pete-restall/KitchenLedStrips/doc/bench/led-data-streams/rgb-000000-noslew-470pF.png

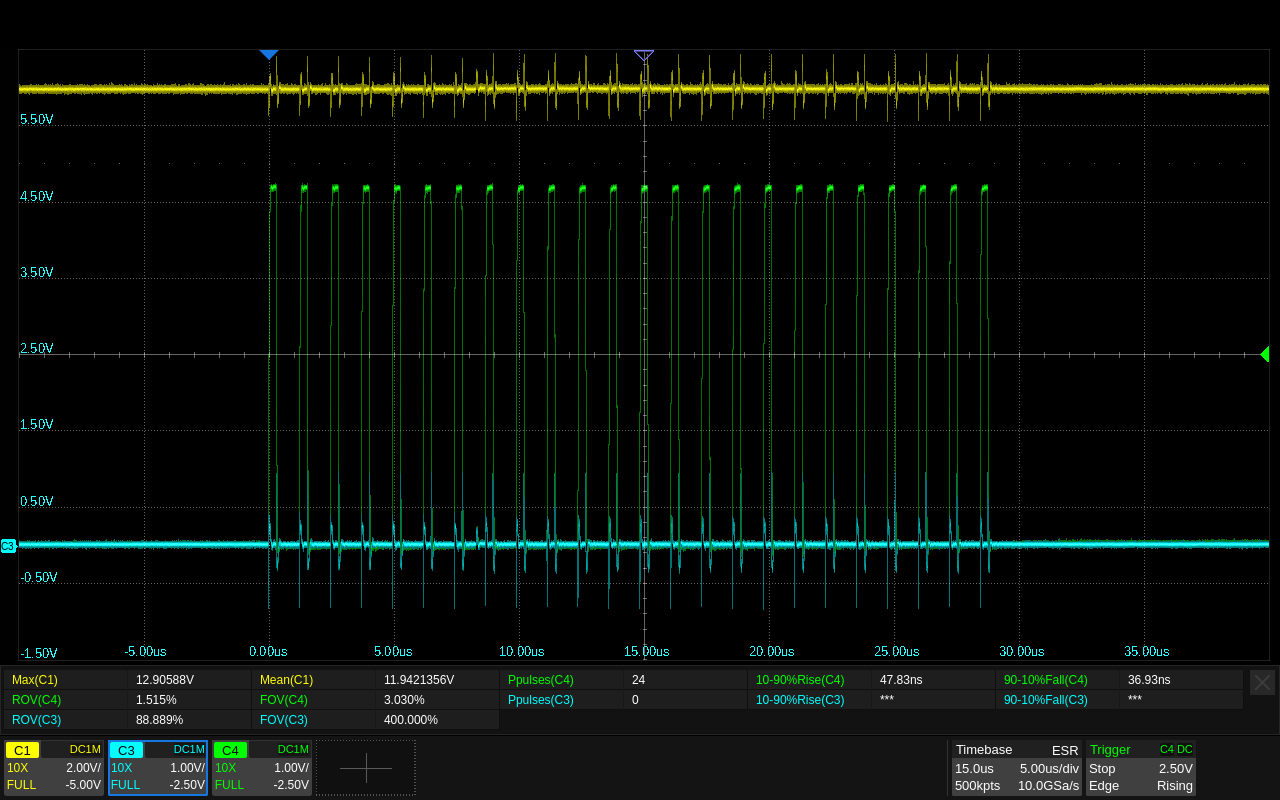
doc/bench/led-data-streams/rgb-000000-noslew-470pF.png
