pete-restall/KitchenLedStrips/doc/bench/led-data-streams/rgb-000000-noslew.png

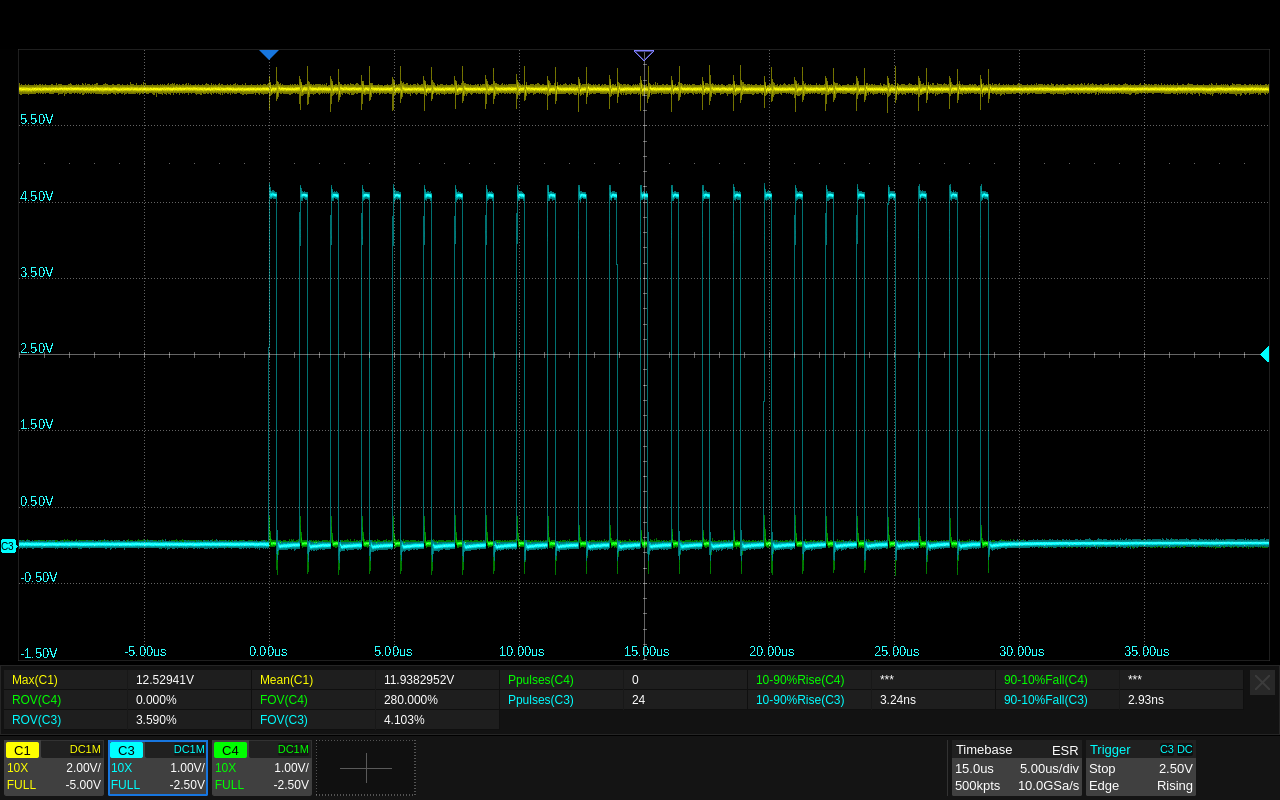
doc/bench/led-data-streams/rgb-000000-noslew.png
