pete-restall/KitchenLedStrips/doc/bench/led-data-streams/rgb-00ff00-noslew.png

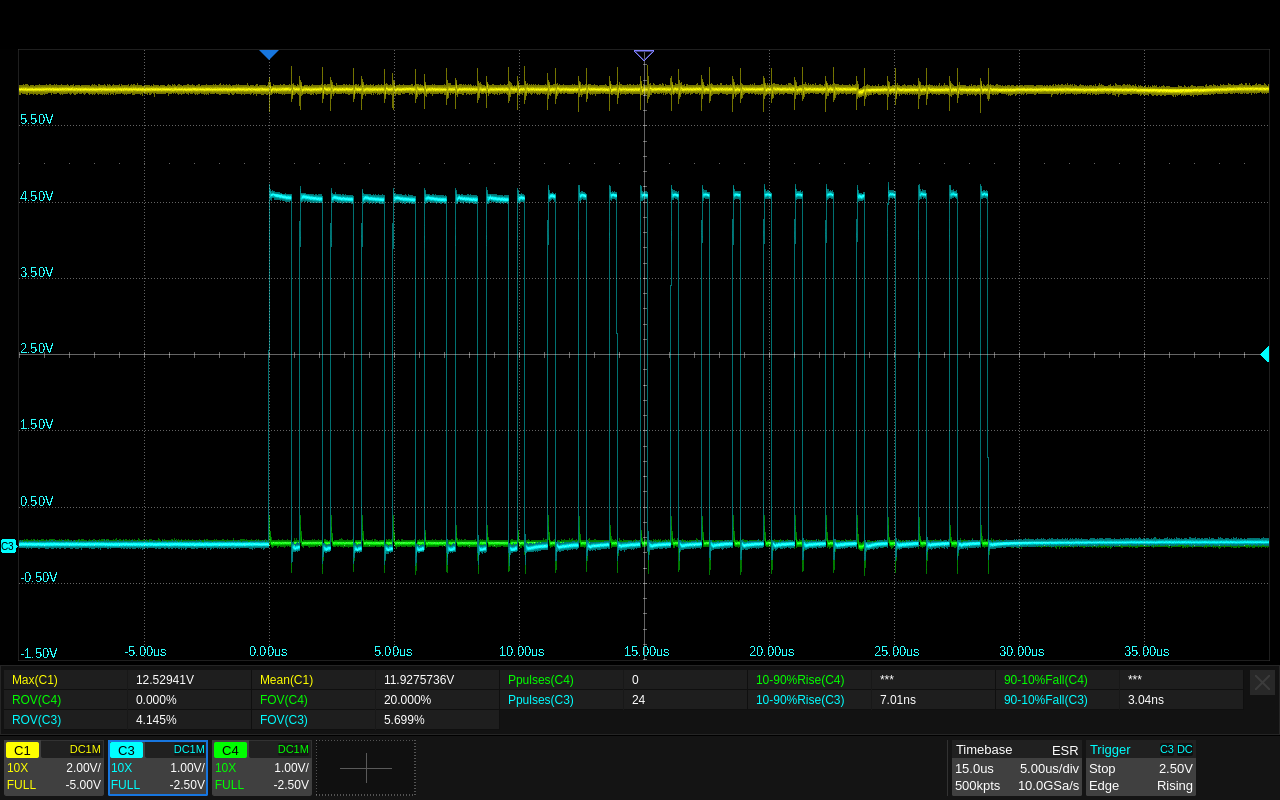
doc/bench/led-data-streams/rgb-00ff00-noslew.png
