pete-restall/KitchenLedStrips/doc/bench/led-data-streams/rgb-00ff00-slew-470pF.png

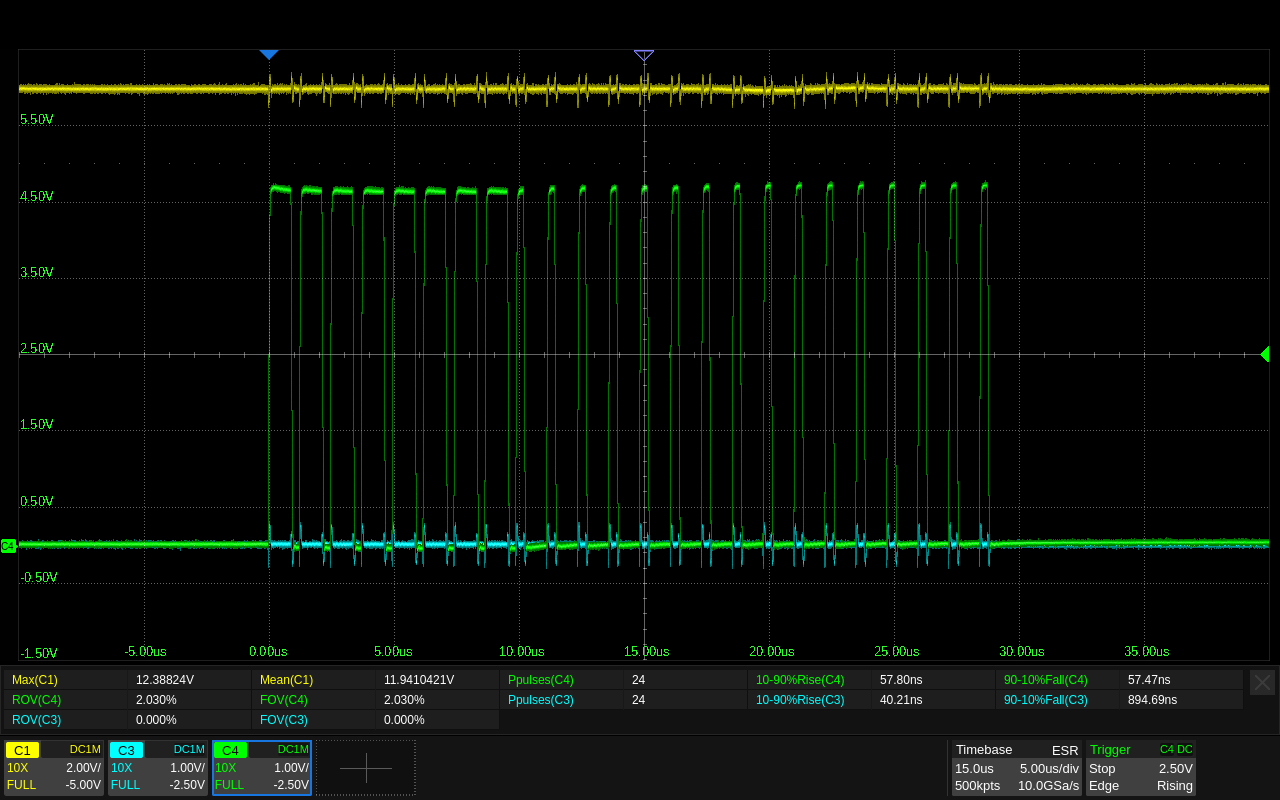
doc/bench/led-data-streams/rgb-00ff00-slew-470pF.png
