pete-restall/KitchenLedStrips/doc/bench/led-data-streams/rgb-0000ff-noslew-470pF.png

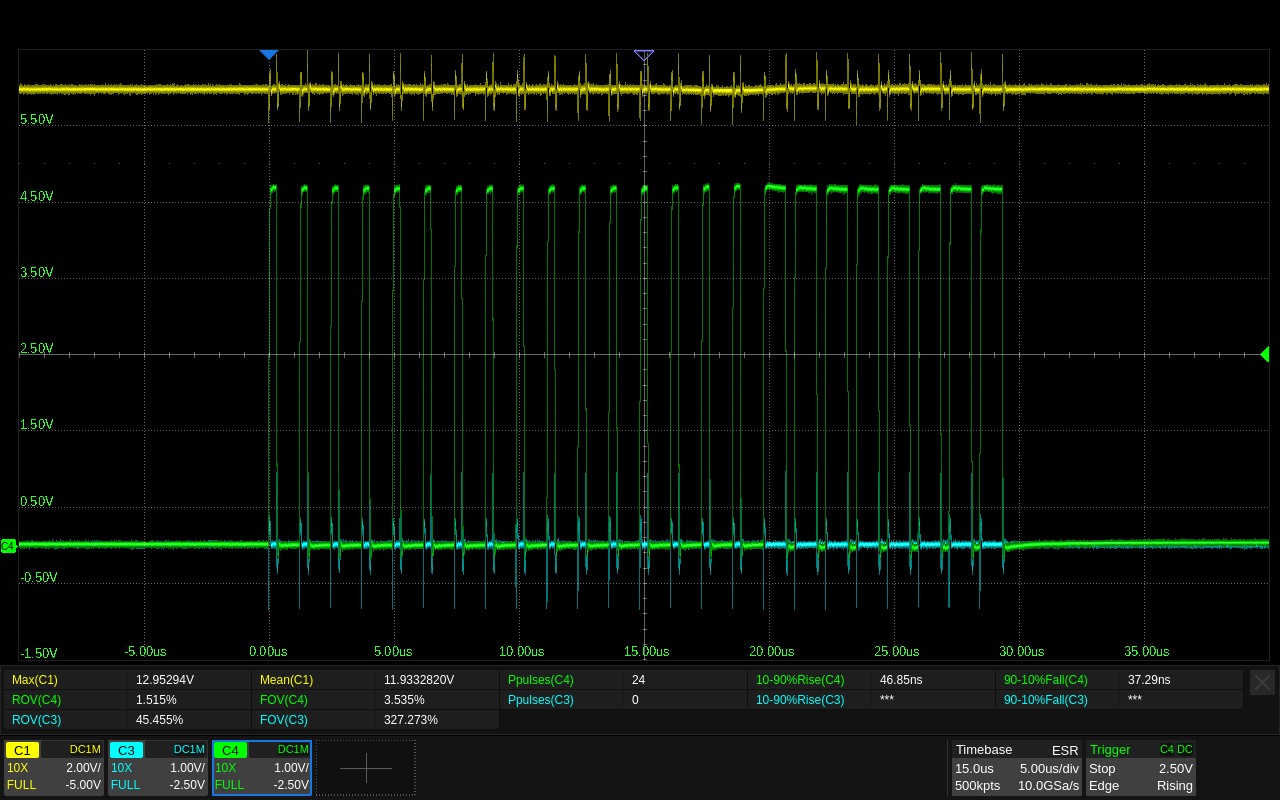
doc/bench/led-data-streams/rgb-0000ff-noslew-470pF.png
