pete-restall/KitchenLedStrips/doc/bench/led-data-streams/rgb-0000ff-noslew.png

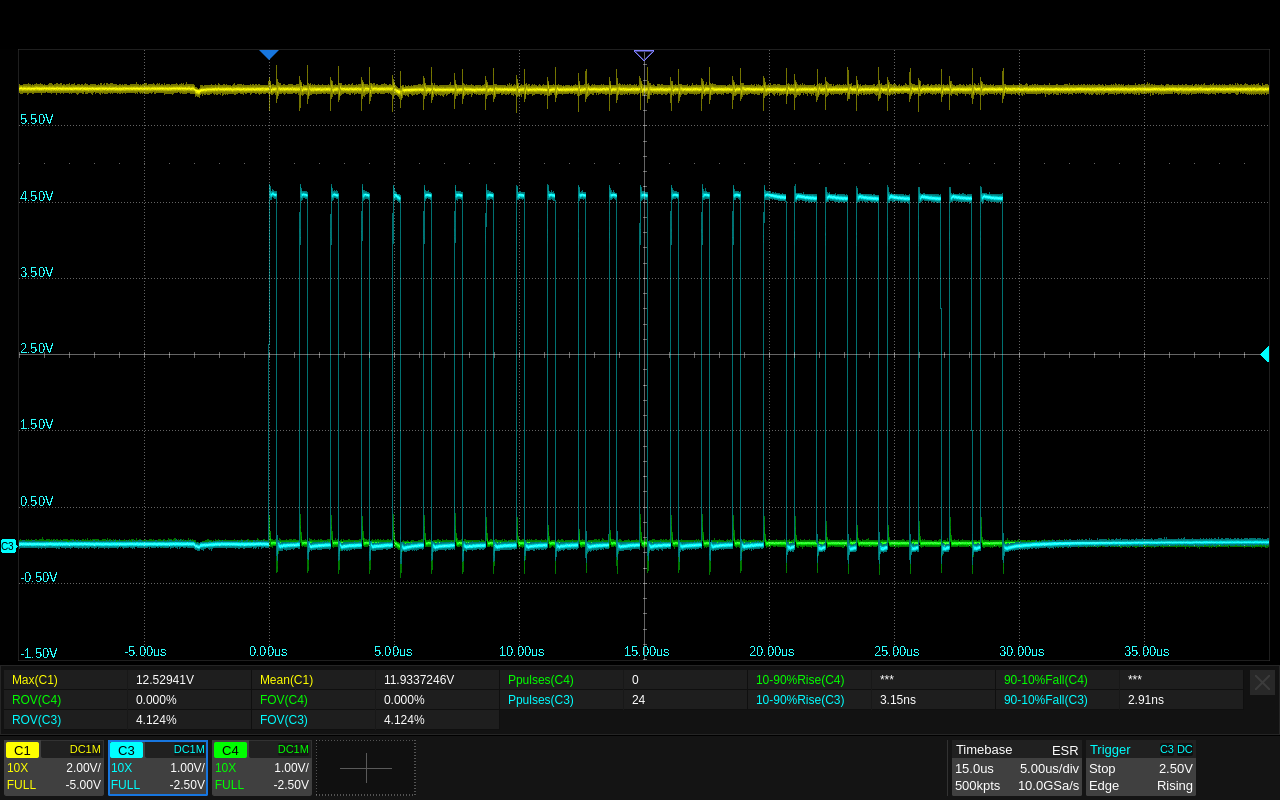
doc/bench/led-data-streams/rgb-0000ff-noslew.png
