pete-restall/KitchenLedStrips/doc/bench/led-data-streams/rgb-ff0000-slew.png

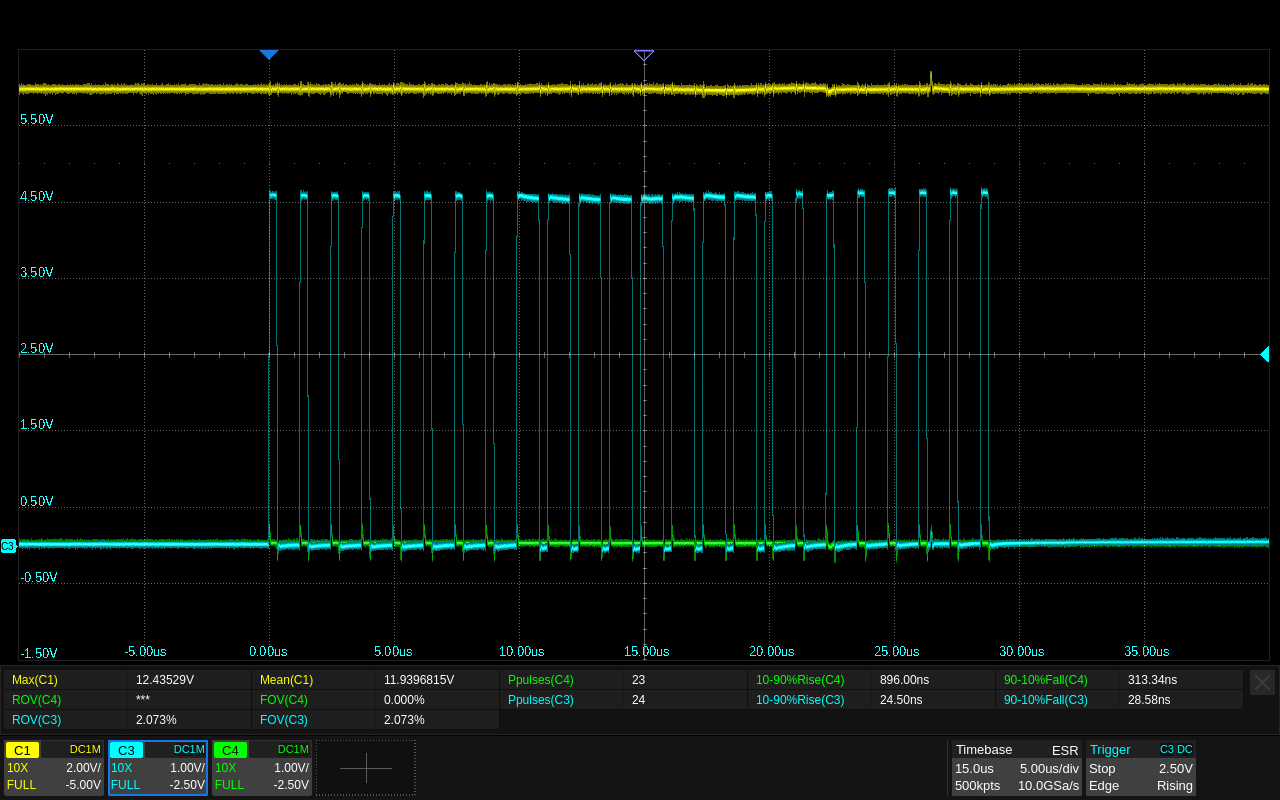
doc/bench/led-data-streams/rgb-ff0000-slew.png
