pete-restall/KitchenLedStrips/doc/bench/led-data-streams/rgb-ffffff-noslew-470pF.png

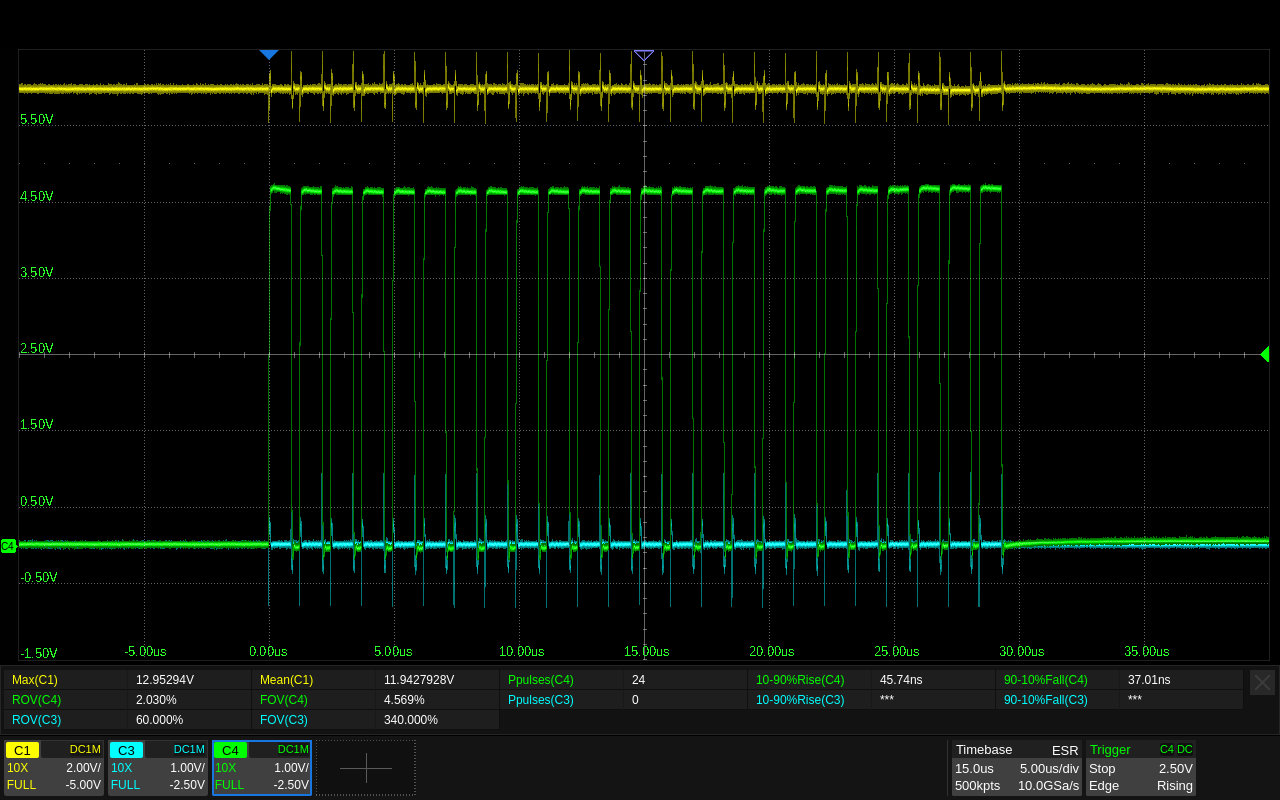
doc/bench/led-data-streams/rgb-ffffff-noslew-470pF.png
