pete-restall/KitchenLedStrips/doc/bench/led-data-streams/rgb-ffffff-noslew.png

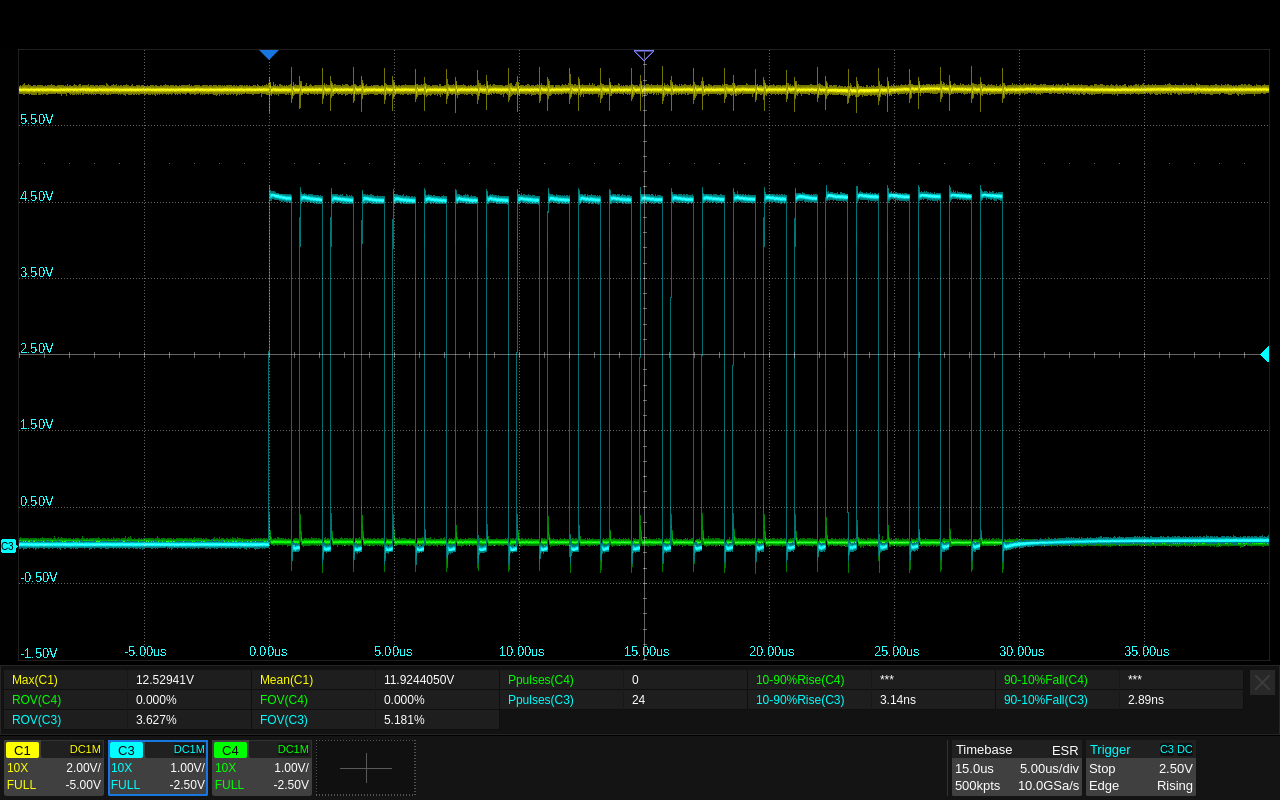
doc/bench/led-data-streams/rgb-ffffff-noslew.png
