pete-restall/KitchenLedStrips/doc/datasheets/pcb/JLC04161H-7628.png

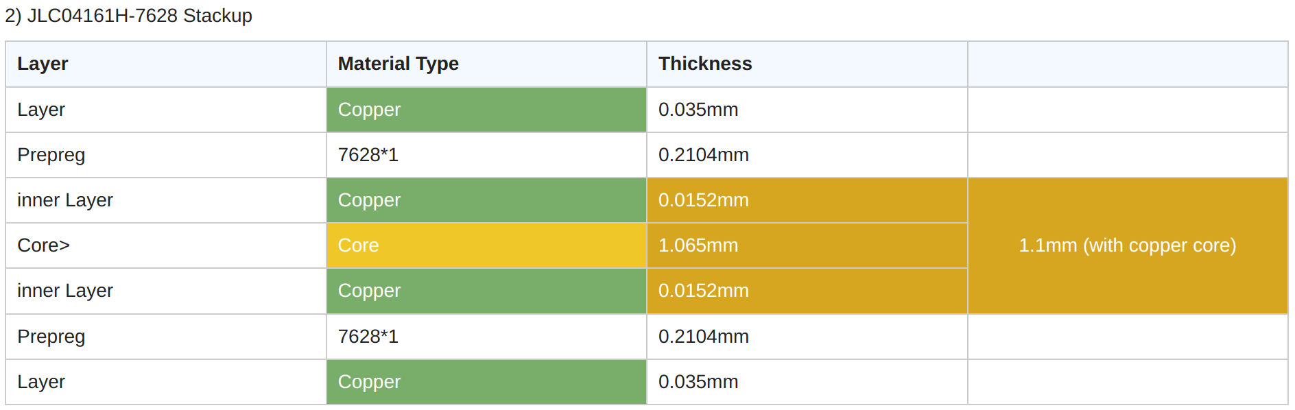
doc/datasheets/pcb/JLC04161H-7628.png
