pete-restall/KitchenLedStrips/sim/pic16f15356-ws2812b-cable-driver/pic16f15356-ws2812b-cable-driver.cir

[Main]
FileType=CIR
Version=12.00
Program=Micro-Cap
Component Version=10.00
Shape Version=11.00
Screen=1920,1080
MCAPVersion=12.2.0.5
Key ID=Demo
NLCnt=68
TXCnt=9

[shapedef]
Name=Buf.root
Line=8,-16,8,16
Line=8,-16,40,0
Line=8,16,40,0
Line=0,0,8,0
Line=40,0,48,0

[shapedef]
Name=Capacitor
Line=0,0,22,0
Line=22,-8,22,8
Line=26,-8,26,8
Line=26,0,48,0
Current=32,12,16,12

[shapedef]
Name=Ground
Line=0,0,12,0
Line=12,-8,12,8
Line=18,-4,18,4
Line=24,0,24,0

[shapedef]
Name=IBIS_Out5
Root="Buf.root",0,0,0
Line=32,-16,32,-4
Line=32,4,32,16
Root="Plus.root",38,-12,0
Root="Minus.root",38,12,0
Line=24,-16,24,-8

[shapedef]
Name=Inductor
Line=42,0,48,0
Line=0,0,5,0
Arc=5,-7,17,7 , 11,-7,5,0
Arc=13,-7,25,7 , 19,-7,13,0
Arc=29,-7,41,7 , 35,-7,29,0
Arc=21,-7,33,7 , 27,-7,21,0
Arc=6,-7,18,7 , 18,0,12,-7
Arc=14,-7,26,7 , 26,0,20,-7
Arc=22,-7,34,7 , 34,0,28,-7
Arc=30,-7,42,7 , 42,0,36,-7
Line=11,-7,12,-7
Line=19,-7,20,-7
Line=27,-7,28,-7
Line=35,-7,36,-7
Arc=13,-4,17,2 , 13,-1,15,2
Arc=29,-4,33,2 , 29,-1,31,2
Arc=21,-4,25,2 , 21,-1,23,2
Arc=14,-4,18,2 , 16,2,18,-1
Arc=30,-4,34,2 , 32,2,34,-1
Arc=22,-4,26,2 , 24,2,26,-1
Line=15,2,16,2
Line=23,2,24,2
Line=31,2,32,2
Line=5,5,9,5
Line=41,5,41,9
Line=39,7,43,7
Current=32,8,16,8

[shapedef]
Name=Lines
Line=56,0,48,0
Arc=0,-12,8,12 , 0,0,4,12
Arc=0,-12,8,12 , 4,-12,0,0
Arc=0,-12,8,12 , 4,12,8,0
Arc=0,-12,8,12 , 8,0,4,-12
Arc=40,-12,48,12 , 48,0,44,-12
Arc=40,-12,48,12 , 44,12,48,0
Line=4,0,-8,0
Line=4,-12,44,-12
Line=4,12,44,12
Line=-8,48,4,48
Line=4,12,4,48
Line=44,12,44,48
Line=44,48,56,48
Current=-8,8,0,8
Current=56,8,48,8

[shapedef]
Name=Minus.root
Line=-2,0,2,0

[shapedef]
Name=Plus.root
Line=-2,0,2,0
Line=0,-2,0,2

[shapedef]
Name=Pulse_Source
Root="Vsource.root",0,0,0
Line=20,-4,20,0
Line=20,0,26,0
Line=26,0,26,4

[shapedef]
Name=Resistor
PolyOpen=12
PolyLine=0,0
PolyLine=0,0
PolyLine=12,0
PolyLine=14,-4
PolyLine=18,4
PolyLine=22,-4
PolyLine=26,4
PolyLine=30,-4
PolyLine=34,4
PolyLine=36,0
PolyLine=48,0
PolyLine=48,0
Current=32,8,16,8

[shapedef]
Name=SPICE_V
Root="Vsource.root",0,0,0

[shapedef]
Name=Vsource.root
Line=0,0,12,0
Line=36,0,48,0
Ellipse=12,-12,36,12
FColor=None
Line=7,5,7,9
Root="Plus.root",41,7,0
Current=32,16,16,16

[compdef]
Name=Resistor
Definition=Resistor
Shape=Resistor
Mask=6913
Used=167
memo=Resistor
Label Offset=18,6,8,11
PinCnt=2
Pin="Plus",6,0,-10,-4
Pin="Minus",0,0,-14,-4

[compdef]
Name=Ground
Definition=Ground
Shape=Ground
Mask=1793
Used=288
memo=Ground
Label Offset=0,0,0,0
PinCnt=1
Pin="PinA",0,0,-3,-7

[compdef]
Name=Voltage Source
Definition=VSpice
Shape=SPICE_V
Mask=4865
Used=52
memo=Voltage Source
Label Offset=19,13,15,13
PinCnt=2
Pin="Plus",6,0,-5,-6
Pin="Minus",0,0,-20,-6

[compdef]
Name=Pulse Source
Definition=Pulse source
Shape=Pulse_Source
Mask=4864
Used=7
memo=Pulse Source
Label Offset=18,13,15,9
PinCnt=2
Pin="Plus",6,0,-5,-4
Pin="Minus",0,0,-19,-4

[compdef]
Name=Capacitor
Definition=Capacitor
Shape=Capacitor
Mask=7425
Used=27
memo=Capacitor
Label Offset=16,12,12,12
PinCnt=2
Pin="Plus",6,0,-3,-5
Pin="Minus",0,0,-14,-5

[compdef]
Name=IBIS_Output5
Definition=Subckt
Shape=IBIS_Out5
Mask=4112
Used=7
memo=Output IBIS Model with Power Supplies uses an IBIS file
Label Offset=43,7,8,41
PinCnt=5
Pin="In",a,0,0,-4,15
Pin="En",a,3,-2,-15,-1
Pin="Vcc",a,4,-2,4,1
Pin="Vee",a,4,2,5,14
Pin="Out",a,6,0,-5,-2

[compdef]
Name=TLine
Definition=Tline
Shape=Lines
Mask=5632
Used=4
memo=Transmission Line - Ideal or Lossy
Label Offset=10,15,-8,12
PinCnt=4
Pin="A+",-1,0,-10,-5
Pin="A-",-1,6,-11,18
Pin="B+",7,0,0,-5
Pin="B-",7,6,-6,18

[compdef]
Name=Inductor
Definition=Inductor
Shape=Inductor
Mask=7681
Used=39
memo=Inductor
Label Offset=18,9,11,12
PinCnt=2
Pin="Plus",6,0,-5,-9
Pin="Minus",0,0,-3,-9

[Circuit]
Window Placement=2,3, -1,-1, -8,-31, 52,52,1507,628
Default Object=Color=#000080
Default Object Font=Height=-15,FStyle=0,Color=#000080,Name=Arial
Default Object Apply Border To Text=No
Default Object Apply Fill To Text=No
Default Object GridSnap=No
NodeVoltageFormat=3
CurrentFormat=3
PowerFormat=3
PathDelayFormat=3
WarningFormat=3
GridTextFormulaFormat=3
Window Placement in Transient Analysis=2,3, -1,-1, -8,-31, 78,78,1729,654
SpiceType=AMBIGUOUS
Title_Block_Border=None
Title_Block=False
Show Nodes=False
Show Voltages=False
Show Current=False
Show Power=False
Show Condition=False
Show Pin Connections=False
Show Connection Warnings=False
Show Cross=False
Show Attribute Text=True
Show Grid Text=True

[Comp]
Name=Resistor
Px=240,96
Rot=6

[Attr]
ON=-33,-37,PART
V=R2
Style=8192

[Attr]
ON=-33,-23,RESISTANCE
V=91
Style=8192

[Attr]
ON=0,0,PACKAGE
V

[Wire]
Pxs=240,96,256,96

[Wire]
Pxs=368,176,376,176

[Comp]
Name=Ground
Px=176,112
Rot=7

[Comp]
Name=Voltage Source
Px=32,56
Rot=3

[Attr]
ON=-31,-27,PART
V=V2
Style=8192

[Attr]
ON=-32,-41,VALUE
V=DC 5 AC 1 0

[Attr]
ON=0,0,PACKAGE
V

[Attr]
ON=0,0,Saved_Pulse
V=DC 3.3 AC 1 0 Pulse 0 5 100n 10n 10n 400n 1u
Style=256

[Attr]
ON=0,0,Saved_None
V=DC 5 AC 1 0
Style=256

[Comp]
Name=Ground
Px=32,56
Rot=7

[Wire]
Pxs=176,8,176,80

[Comp]
Name=Pulse Source
Px=32,144
Rot=3

[Attr]
ON=-31,-23,PART
V=V1
Style=8192

[Attr]
ON=-32,-37,MODEL
V=SQUARE

[Attr]
ON=0,0,PACKAGE
V

[Comp]
Name=Ground
Px=32,144
Rot=7

[Wire]
Pxs=32,96,72,96

[Comp]
Name=Resistor
Px=800,232
Rot=5

[Attr]
ON=8,-25,PART
V=R1
Style=8192

[Attr]
ON=8,-39,RESISTANCE
V=1Meg
Style=8192

[Attr]
ON=0,0,PACKAGE
V

[Comp]
Name=Ground
Px=800,232
Rot=7

[Wire]
Pxs=800,176,800,184

[Comp]
Name=Capacitor
Px=432,232
Rot=5

[Attr]
ON=12,-26,PART
V=C1
Style=8192

[Attr]
ON=12,-40,CAPACITANCE
V=20p
Style=8192

[Attr]
ON=0,0,PACKAGE
V

[Comp]
Name=Ground
Px=432,232
Rot=7

[Wire]
Pxs=800,176,856,176

[Wire]
Pxs=432,176,432,184

[Wire]
Pxs=128,96,144,96

[Wire]
Pxs=256,176,312,176

[Wire]
Pxs=32,8,104,8

[Wire]
Pxs=168,56,168,80

[Wire]
Pxs=32,56,56,56

[Wire]
Pxs=72,96,72,176

[Comp]
Name=IBIS_Output5
Px=144,96

[Attr]
ON=43,7,PART
V=X2
Style=8192

[Attr]
ON=43,21,NAME
V=IO_DIG_8_TYP

[Attr]
ON=0,0,PACKAGE
V

[Comp]
Name=IBIS_Output5
Px=144,176

[Attr]
ON=43,7,PART
V=X3
Style=8192

[Attr]
ON=43,21,NAME
V=IO_DIG_8_TYP

[Attr]
ON=0,0,PACKAGE
V

[Comp]
Name=IBIS_Output5
Px=144,256

[Attr]
ON=43,7,PART
V=X4
Style=8192

[Attr]
ON=43,21,NAME
V=IO_DIG_8_TYP

[Attr]
ON=0,0,PACKAGE
V

[Wire]
Pxs=72,176,144,176

[Wire]
Pxs=72,256,144,256

[Wire]
Pxs=56,232,168,232

[Wire]
Pxs=72,96,128,96

[Wire]
Pxs=72,176,72,256

[Wire]
Pxs=256,96,256,176

[Comp]
Name=Resistor
Px=240,176
Rot=6

[Attr]
ON=-33,-37,PART
V=R3
Style=8192

[Attr]
ON=-33,-23,RESISTANCE
V=91
Style=8192

[Attr]
ON=0,0,PACKAGE
V

[Comp]
Name=Resistor
Px=240,256
Rot=6

[Attr]
ON=-33,-37,PART
V=R4
Style=8192

[Attr]
ON=-33,-23,RESISTANCE
V=91
Style=8192

[Attr]
ON=0,0,PACKAGE
V

[Wire]
Pxs=240,256,256,256

[Wire]
Pxs=256,176,256,256

[Wire]
Pxs=240,176,256,176

[Comp]
Name=Ground
Px=176,192
Rot=7

[Comp]
Name=Ground
Px=176,272
Rot=7

[Wire]
Pxs=168,152,168,160

[Wire]
Pxs=56,152,168,152

[Wire]
Pxs=56,56,56,152

[Wire]
Pxs=56,56,168,56

[Wire]
Pxs=56,152,56,232

[Wire]
Pxs=176,136,176,160

[Wire]
Pxs=104,136,176,136

[Wire]
Pxs=104,8,104,136

[Wire]
Pxs=104,8,176,8

[Wire]
Pxs=168,232,168,240

[Wire]
Pxs=176,216,176,240

[Wire]
Pxs=104,216,176,216

[Wire]
Pxs=104,136,104,216

[Wire]
Pxs=688,176,800,176

[Comp]
Name=Capacitor
Px=856,232
Rot=5

[Attr]
ON=12,-26,PART
V=C2
Style=8192

[Attr]
ON=12,-40,CAPACITANCE
V=1n
Style=8192

[Attr]
ON=0,0,PACKAGE
V

[Comp]
Name=Ground
Px=856,232
Rot=7

[Wire]
Pxs=856,176,856,184

[Wire]
Pxs=856,176,864,176

[Comp]
Name=TLine
Px=680,176
Rot=6

[Attr]
ON=-25,15,PART
V=T2
Style=8192

[Attr]
ON=-26,29,VALUE
V=Len=3 R=22m L=380n C=237p

[Attr]
ON=0,0,PACKAGE
V

[Comp]
Name=Ground
Px=624,224
Rot=7

[Comp]
Name=Ground
Px=688,224
Rot=7

[Wire]
Pxs=544,176,624,176

[Comp]
Name=Inductor
Px=544,176
Rot=6

[Attr]
ON=-33,9,PART
V=L2
Style=8192

[Attr]
ON=-50,23,INDUCTANCE
V=38n
Style=8192

[Attr]
ON=0,0,PACKAGE
V

[Wire]
Pxs=432,176,496,176

[Comp]
Name=TLine
Px=368,176
Rot=6

[Attr]
ON=-25,15,PART
V=T3
Style=8192

[Attr]
ON=-26,29,VALUE
V=Len=6 R=1m L=6.4043n C=0.5267p

[Attr]
ON=0,0,PACKAGE
V

[Comp]
Name=Ground
Px=312,224
Rot=7

[Comp]
Name=Ground
Px=376,224
Rot=7

[Wire]
Pxs=376,176,432,176

[Wire]
Pxs=312,176,320,176

[Grid Text]
Text="vout_b"
Px=864,176
GridSnap=True
JustifyH=Left
JustifyV=Bottom
CBorder=None

[Grid Text]
Text="vin"
Px=128,96
GridSnap=True
JustifyH=Left
JustifyV=Bottom
CBorder=None

[Grid Text]
Text="vout_a"
Px=256,176
GridSnap=True
JustifyH=Left
JustifyV=Bottom
CBorder=None

[Grid Text]
Text="Z=40"
Px=640,160
GridSnap=True
JustifyH=Left
JustifyV=Bottom
CBorder=None

[Grid Text]
Text="18mil PCB Trace 1.6mm FR-4, Z=110"
Px=280,136
GridSnap=True
JustifyH=Left
JustifyV=Bottom
CBorder=None

[Grid Text]
Text="TVS C"
Px=416,160
GridSnap=True
JustifyH=Left
JustifyV=Bottom
CBorder=None

[Grid Text]
Text="Panel Wire"
Px=504,160
GridSnap=True
JustifyH=Left
JustifyV=Bottom
CBorder=None

[Grid Text]
Text="3m of 1mm^2 4-core shielded CY cable"
Px=608,136
GridSnap=True
JustifyH=Left
JustifyV=Bottom
CBorder=None

[Grid Text]
Text="Add discrete capacitance at LED input to dampen oscillations."
Px=912,216
GridSnap=True
JustifyH=Left
JustifyV=Bottom
CBorder=None

[Schematic]
CurrentSection 0=0
CurrentSection 1=0
CurrentSection 2=0
CurrentSection 3=0
Splitter.xs=0
Splitter.ys=0
TextQuad=4099
Scale=0.66666666666666663
GridUser=10
ShapeGroups="Main","Euro","Polarity","Main1","Main11","Electrolytic","GroundArrow","DeMorgan"
CalcRMS=False
CalcAVG=False
CalcPeak=False
CalcVoltage=True
DisplayMeasure=Last
ShareScales=True

[Tools]
Pos=Top
FILESAVEASOLD=No
BOM=No
FILEPCB=No
PROBE=Yes
SELECT=Yes
PAN=Yes
COMP=Yes
TEXT=Yes
WIRE=Yes
WIRED=Yes
BUS=Yes
GRAPHIC=Yes
FLOWCHART=Yes
LINE=No
ELLIPSE=No
RECT=No
DIAM=No
ARC=No
PIE=No
TRIANGLE=No
STAR=No
LEFTBRK=No
RIGHTBRK=No
BOTHBRK=No
META=Yes
PARALLELOGRAM=No
FC_PROCESS=No
FC_ALT_PROCESS=No
FC_DECISION=No
FC_DATA=No
FC_PREDEFPROCESS=No
FC_INTERNALSTORAGE=No
FC_DOCUMENT=No
FC_MULTIDOCUMENT=No
FC_TERMINATOR=No
FC_PREPARATION=No
FC_MANUALINPUT=No
FC_MANUALOPERATION=No
FC_CONNECTOR=No
FC_OFFPAGECONNECTOR=No
FC_PUNCHCARD=No
FC_PUNCHEDTAPE=No
FC_SUMMING_JUNCTION=No
FC_OR=No
FC_COLLATE=No
FC_SORT=No
FC_EXTRACT=No
FC_MERGE=No
FC_STORED_DATA=No
FC_DELAY=No
FC_SAS=No
FC_MAGNETIC_DISK=No
FC_DAS=No
FC_DISPLAY=No
SPREAD_SHEET=Yes
POLYCLOS=No
POLYOPEN=No
FLAG=Yes
INFO=Yes
HELP=Yes
HELP_SPICE=No
LINK=Yes
CHECK=Yes
REGION_ENABLE=Yes
TITLE_BLOCK=Yes
DIGTRC=No
DIGTRC2=No
BUILD_COMMAND=Yes
DIGALL=No
GRIDTEXT=Yes
COMPTEXT=Yes
NODE=Yes
MEASURED=Yes
NODEV=Yes
CURRENT=Yes
POWER=Yes
CONDITIN=Yes
PIN=Yes
CONNWARN=Yes
CROSS=Yes
GRID=Yes
BORDER=Yes
BORDERONE=Yes
TITLE=Yes
RUBBER=Yes
PROPERTY=Yes
STEP=Yes
MIRROR=Yes
ROTATE=Yes
FLIPY=Yes
FLIPX=Yes
CIR_MAKEMACRO=No
CLEARCUTWIRE=No
CLIPBOARDCIRPAGE2BMM=No
FINDCOMP=Yes
FIND=Yes
REPEAT=No
REPLACE=No
MODEL=Yes
CIR2CKT=Yes
ATTDISP=Yes
ENABLE=Yes
DISABLE=Yes
ENABLE_WITH=Yes
TOFRONT=Yes
TOBACK=Yes
SELNEXT=Yes
PAGEADD=Yes
PAGEADDTEXT=No
ADDSECTION=No
PAGEDEL=Yes
ZOOMIN=Yes
ZOOMOUT=Yes
AUTOSCALECIR=Yes
GOTOFLAG=Yes
UPLEVEL=Yes
COLOR=Yes
FONT=Yes
STYLE=Yes
DM_LAST=No
DM_RMS=No
DM_AVG=No
DM_PEAK=No
GRID_NONE=No
GRID_NORMAL=No
GRID_BOLD_5=No
GRID_BOLD_6=No
GRID_BOLD_USER=No
GRAPH_PAPER=No
SPLITCIRTEXTH=No
SPLITCIRTEXTV=No
SPACE_SPLITTERS_EVENLY=No
NORMALCIR=No
RENAMEDEFINE=No
RENAMECMP=No
ATTALIGN=No
RESETNODEPOS=No
FIT2STANDARD=No
NODESNAP=No
MOVETEXT=No
TEXTINC=No
TOGGLETEXT=No
TOGGLEMODE=No
TOLERANCE=No
ALIGNAB=No
ALIGNLEFT=Yes
ALIGNCENTER=Yes
ALIGNRIGHT=Yes
ALIGNTOP=Yes
ALIGNMIDDLES=Yes
ALIGNBOTTOM=Yes

[Section]
Index=0
Name="pic16f15356-ws2812b-cable-driver"
Type=Main
Enable=True
CurrentPage 0=0
CurrentPage 1=0
CurrentPage 2=0
CurrentPage 3=0
TabSize 0=425
TabSize 1=425
TabSize 2=425
TabSize 3=425

[Page]
Index=0
Section=0
Print=True
Enable=True
Name=Main
PrinterScale=1
Scale 0=1
Scale 1=1
Scale 2=1
Scale 3=0.66666666666666663
Px=440,307
WinBackGround Color=#FFFFFF
Select Color=#FF0000
Anchor Color=#000000
Select Box Color=#000080
Grid Text Color=Height=-12,FStyle=0,Color=#0000FF,Name=Verdana
Grid Text RTF=False
Grid Text Angle=0
Grid Text GridSnap=True
Grid Text PinIt=False
Grid Text JustifyH=Left
Grid Text JustifyV=Bottom
Grid GradientColor2=None
Grid OutlineThickness=1
Grid OutlineColor=None
Component Color=#0000FF
Attribute Text=Height=-12,FStyle=0,Color=#008000,Name=Verdana
Wire Color=#008000
Bus Color=#008000
Pin Connection=Height=-10,FStyle=0,Color=#FF0000,Name=Arial
Pin Marker Color=#008000
Node Number=Height=-11,FStyle=0,Color=#FF00FF,Name=Arial
Node Voltage Color=Height=-11,FStyle=0,Color=#000000,Name=Arial
Dynamic AC Voltage Color=#E4E4E4
Text Banner Text=Height=-15,FStyle=0,Color=#800000,Name=Arial
Title Block Background=#C0C0C0
Current=Height=-11,FStyle=0,Color=#0000FF,Name=Arial
Power/Condition=Height=-11,FStyle=0,Color=#FF0000,Name=Arial
Digital Path Color=#FF0000
Title Block Border=#000000
Disabled	Color=#C0C0C0
Search Color=#FFFF00
Grid Color=#000000
Graph Paper=#E4E4E4
Digital 0 Color=#000000
Digital R Color=#FFFF00
Digital F Color=#FFFF00
Digital 1 Color=#FF0000
Digital X Color=#C0C0C0
Digital Z Color=#808080
Block Select Color=#51F998

[Page]
Index=1
Section=0
Type=Text
Print=False
Enable=True
Name=Text
Font=Height=-15,FStyle=0,Color=#000000,Name=Courier New
Comment Color=#008000
WinBackGround Color=#FFFFFF
Disabled	Color=#C0C0C0
KeyWord Color=#0000FF
Error	Color=#FF0000
Search Color=#FFFF00

[Page]
Index=2
Section=0
Type=Text
Print=False
Enable=True
Name=Models
Font=Height=-15,FStyle=0,Color=#000000,Name=Courier New
Comment Color=#008000
WinBackGround Color=#FFFFFF
Disabled	Color=#C0C0C0
KeyWord Color=#0000FF
Error	Color=#FF0000
Search Color=#FFFF00

[Page]
Index=3
Section=0
Type=Info
Print=False
Enable=True
Name=Info
Font=Height=-15,FStyle=0,Color=#000000,Name=Courier New
Comment Color=#008000
WinBackGround Color=#FFFFFF
Disabled	Color=#C0C0C0
KeyWord Color=#0000FF
Error	Color=#FF0000
Search Color=#FFFF00

[Text Area]
Section=0
Page=1

[Text Area]
Section=0
Page=2
Text=* Schematic File
Text=*
Text=* Syntax:
Text=* .MODEL <model name> [AKO:<reference model name>] <ModelType>
Text=* +([<parameter name>=<value>][LOT[/#][/GAUSS|/UNIFORM|/WCASE]=[<tol>[%]] |[-<low>%,<high>%]][DEV[/#][/GAUSS|/UNIFORM|/WCASE]=[<tol>[%]]...)
Text=* ModelType must be one of OPA,D,NPN,NMOS,NJF,PUL,SIN,TRN,CORE,GASFET,VSWITCH,ISWITCH,CAP,IND,RES,PNP,PMOS,PJF,DOUTPUT,DINPUT,UADC,UDAC,UGATE,UTGATE,UEFF,UGFF,UDLY,UPLD,UROM,URAM,UBGT,UIO,LPNP,NIGBT,I,V
Text=*
Text=*Examples:
Text=* .MODEL 2N2222A NPN(BF=150 IS=1E-14)
Text=* .model M1 NMOS(KP=2.5E-5 VTO=1.345 CGDO=14.67p CGBO=4.566p)
Text=* .MODEL DK D(IS=1E-18)
Text=* .model 2N2222A AKO:2N2222 NPN (BF=55 ISE=10F)
Text=* .Model BJT1 NPN (RE=12 LOT/1/GAUSS=30% DEV/2/UNIFORM=2%)
Text=*
Text=* A .cir file is typically found in the data directory
Text=*
Text=*** From file C:\Program Files\Micro-Cap-12\library\UTILITY.LBR
Text=*** 5V Square Wave
Text=.MODEL SQUARE PUL (P1=0 P2=1n P3=625n P4=626n P5=1.25u)
Text=*
Text=* Ver:          4.2
Text=* Name:         PIC16F15356_uqfn28.ibs
Text=* Rev:          1.0
Text=* Date:         October 21, 2020
Text=* Source:       File originated at Microchip
Text=* Notes:        The following is an IBIS list for the PIC16F15356.
Text=* Disclaimer:   Property of Microchip technology Incorporated.
Text=*
Text=* Component:    PIC16F15356
Text=* Manufacturer: MICROCHIP TECHNOLOGY Inc.
Text=*
Text=*
Text=* Output Buffer Models:
Text=*    IO_DIG_8_TYP
Text=*
Text=* Total: 1 Pin Models Created
Text=*
Text=
Text=.SUBCKT IO_DIG_TYP_PULLUP 1 2 3 4
Text=R1 1 2 1
Text=G1 2 1 TABLE {V(3,4)} =
Text=+-5,0.00214698
Text=+-4.93103,0.00214005
Text=+-4.74138,0.00212479
Text=+-4.55172,0.00210953
Text=+-4.36207,0.00208664
Text=+-4.17241,0.00207138
Text=+-3.98276,0.00205612
Text=+-3.7931,0.00203705
Text=+-3.60345,0.00201797
Text=+-3.41379,0.00200081
Text=+-3.22414,0.00198364
Text=+-3.03448,0.00196457
Text=+-2.84483,0.0019474
Text=+-2.65517,0.00192833
Text=+-2.46552,0.00191116
Text=+-2.27586,0.001894
Text=+-2.08621,0.00187492
Text=+-1.89655,0.0018568
Text=+-1.7069,0.00183868
Text=+-1.51724,0.00182152
Text=+-1.32759,0.0025177
Text=+-1.13793,0.00435615
Text=+-0.948276,0.014507
Text=+-0.758621,0.0287074
Text=+-0.568966,0.0213919
Text=+-0.5,0.0186993
Text=+-0.37931,0.0140466
Text=+-0.189655,0.00690623
Text=+-0,-5.80352e-015
Text=+0.172414,-0.00598056
Text=+0.344828,-0.0116055
Text=+0.517241,-0.0168757
Text=+0.689655,-0.0217924
Text=+0.862069,-0.0263564
Text=+1.03448,-0.0305689
Text=+1.2069,-0.0344307
Text=+1.37931,-0.037943
Text=+1.55172,-0.0411066
Text=+1.72414,-0.0439227
Text=+1.89655,-0.0463922
Text=+2.06897,-0.0485161
Text=+2.24138,-0.0502957
Text=+2.41379,-0.0517397
Text=+2.58621,-0.052901
Text=+2.75862,-0.0538525
Text=+2.93103,-0.0546476
Text=+3.10345,-0.0553244
Text=+3.27586,-0.0559109
Text=+3.44828,-0.0564276
Text=+3.62069,-0.0568899
Text=+3.7931,-0.0573092
Text=+3.96552,-0.0576938
Text=+4.13793,-0.0580504
Text=+4.31034,-0.058384
Text=+4.48276,-0.0586986
Text=+4.65517,-0.0589975
Text=+4.82759,-0.0592838
Text=+5,-0.0595605
Text=+5.25172,-0.0599544
Text=+5.50345,-0.060348
Text=+5.75517,-0.0586253
Text=+6.0069,-0.0395914
Text=+6.25862,-0.037817
Text=+6.51034,-0.0378718
Text=+6.76207,-0.0381031
Text=+7.01379,-0.0383663
Text=+7.26552,-0.0386677
Text=+7.51724,-0.0390167
Text=+7.76897,-0.0394173
Text=+8.02069,-0.0398827
Text=+8.27241,-0.0404148
Text=+8.52414,-0.0410271
Text=+8.77586,-0.0417252
Text=+9.02759,-0.0425186
Text=+9.27931,-0.0434189
Text=+9.53103,-0.0444374
Text=+9.78276,-0.0455742
Text=+10,-0.0466705
Text=.ENDS IO_DIG_TYP_PULLUP
Text=
Text=.SUBCKT IO_DIG_TYP_PULLDOWN 1 2 3 4
Text=R1 1 2 1
Text=G1 2 1 TABLE {V(3,4)} =
Text=+-5,-0.00653557
Text=+-4.78276,-0.00646973
Text=+-4.53103,-0.00639343
Text=+-4.27931,-0.00631332
Text=+-4.02759,-0.00623703
Text=+-3.77586,-0.00615692
Text=+-3.52414,-0.00607872
Text=+-3.27241,-0.00599861
Text=+-3.02069,-0.0059166
Text=+-2.76897,-0.00583458
Text=+-2.51724,-0.00575447
Text=+-2.26552,-0.00567055
Text=+-2.01379,-0.00558853
Text=+-1.76207,-0.00550461
Text=+-1.51034,-0.00542021
Text=+-1.25862,-0.00593233
Text=+-1.0069,-0.0126126
Text=+-0.755172,-0.0687654
Text=+-0.503448,-0.0510857
Text=+-0.251724,-0.0258881
Text=+0,-1.78576e-013
Text=+0.172414,0.0172008
Text=+0.344828,0.0330173
Text=+0.517241,0.0475009
Text=+0.689655,0.060701
Text=+0.862069,0.0726643
Text=+1.03448,0.0834355
Text=+1.2069,0.0930569
Text=+1.37931,0.101569
Text=+1.55172,0.109011
Text=+1.72414,0.115418
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
Text=+ (6e-008,0.000664128) (6.1e-008,0.000393584) (6.2e-008,0.000123139) (6.3e-008,-4.01796e-010) (6.4e-008,-4.10475e-010)
Text=+ (6.5e-008,-4.03131e-010) (6.6e-008,-4.13813e-010) (6.7e-008,-4.08472e-010) (6.8e-008,-4.03131e-010) (6.9e-008,-4.13813e-010)
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
