pete-restall/KitchenLedStrips/src/firmware/lights-gadget/src/power-supply/is-enabled.asm

	#include "../mcu.inc"
	#include "power-supply.inc"

	radix decimal

.powersupply code
	global powerSupplyIsEnabled

powerSupplyIsEnabled:
_returnFalseIfNotEnablingPowerSwitch:
	banksel PORTB
	btfss PORTB, RB5
	retlw 0

_returnFalseIfPowerGoodFlagIsLow:
	btfss PORTB, RB4
	retlw 0

_returnFalseIfVoltageRailMonitoringHasNotYetStarted:
	banksel ADCON0
	btfss ADCON0, ADON
	retlw 0

	banksel _powerSupplyBlankingTimer
	movf _powerSupplyBlankingTimer, F
	btfss STATUS, Z
	retlw 0

_powerSupplyIsEnabled:
	retlw 1

	end
