pete-restall/KitchenLedStrips/src/firmware/lights-gadget/src/commands/ir-transceiver/initialise.asm

	#include "../../mcu.inc"
	#include "ir-transceiver.inc"

	radix decimal

.irtransceiver code
	global irTransceiverInitialise

irTransceiverInitialise:
	banksel _irTransceiverLastReceivedByteTimestamp
	clrf _irTransceiverLastReceivedByteTimestamp
	clrf _irTransceiverPollState

	pagesel irTransceiverInitialiseUart2
	call irTransceiverInitialiseUart2

	pagesel _irTransceiverInitialiseTimer1ForDoubledCarrierWave
	call _irTransceiverInitialiseTimer1ForDoubledCarrierWave

	pagesel _irTransceiverInitialiseCcp1ForDoubledCarrierWave
	call _irTransceiverInitialiseCcp1ForDoubledCarrierWave

	pagesel _irTransceiverInitialiseClc2AsModulatedOutput
	call _irTransceiverInitialiseClc2AsModulatedOutput

	pagesel _irTransceiverInitialiseClc3AsUart2TxBodgeWire
	call _irTransceiverInitialiseClc3AsUart2TxBodgeWire

	return

	end
